yanataka60/FM-7_SD/jpeg/FM-7_SD_1.JPG

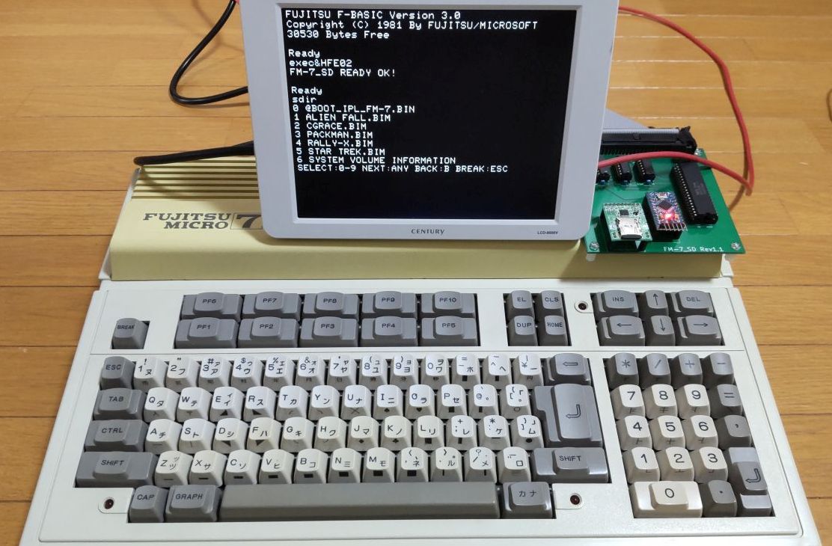
jpeg/FM-7_SD_1.JPG
